me-RK/Wearable-Air-Quality-Pendant/Images/AIQ Monitor Pendant.png

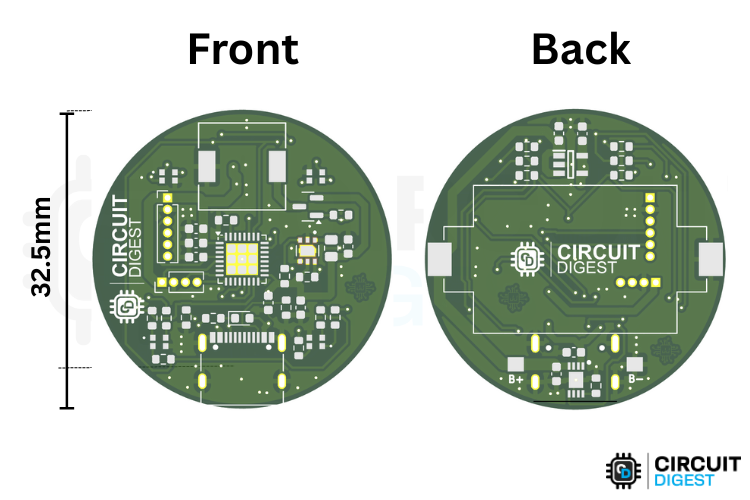
Images/AIQ Monitor Pendant.png
