me-RK/Wearable-Air-Quality-Pendant/Images/RGB Light Circuit &  Buzzer Driver Circuit.png

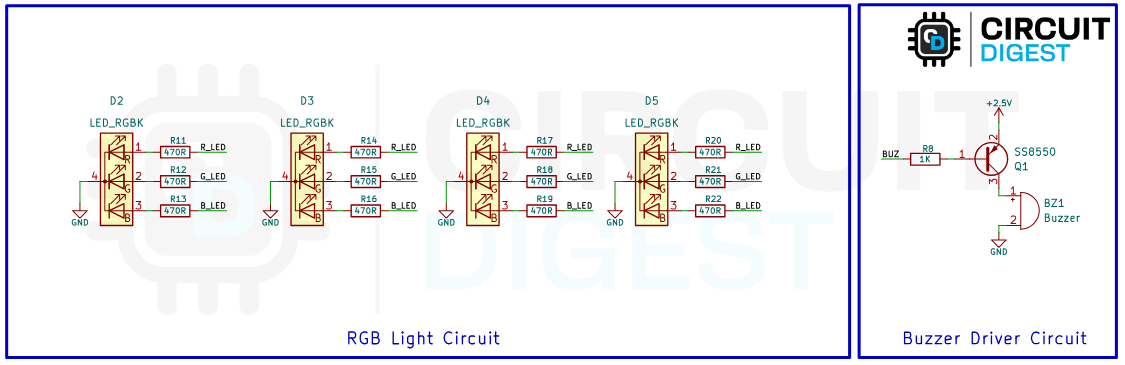
Images/RGB Light Circuit & Buzzer Driver Circuit.png
