me-RK/Wearable-Air-Quality-Pendant/Images/STM32 Programming and IO Circuit.png

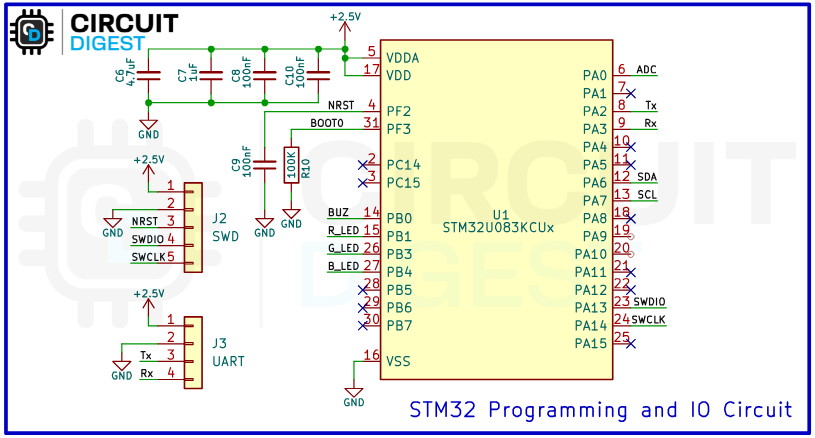
Images/STM32 Programming and IO Circuit.png
