me-RK/Wearable-Air-Quality-Pendant/Images/Title Image.png

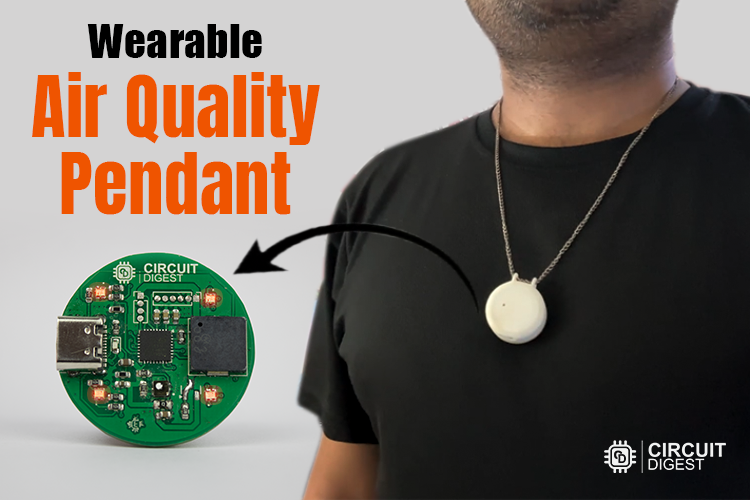
Images/Title Image.png
