me-RK/Wearable-Air-Quality-Pendant/PCB/Wearable-Air-Quality-Pendant/Wearable Air Quality Pendant.png

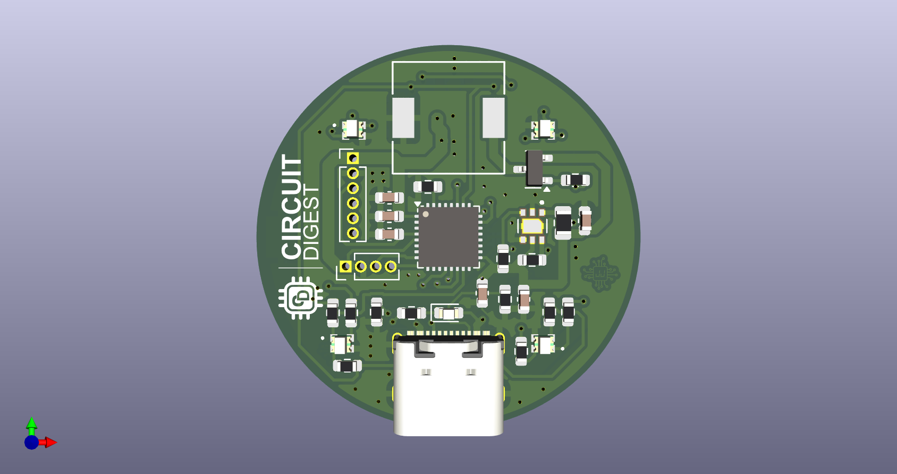
PCB/Wearable-Air-Quality-Pendant/Wearable Air Quality Pendant.png
