me-RK/Wearable-Air-Quality-Pendant/Images/Parts and PCB .png

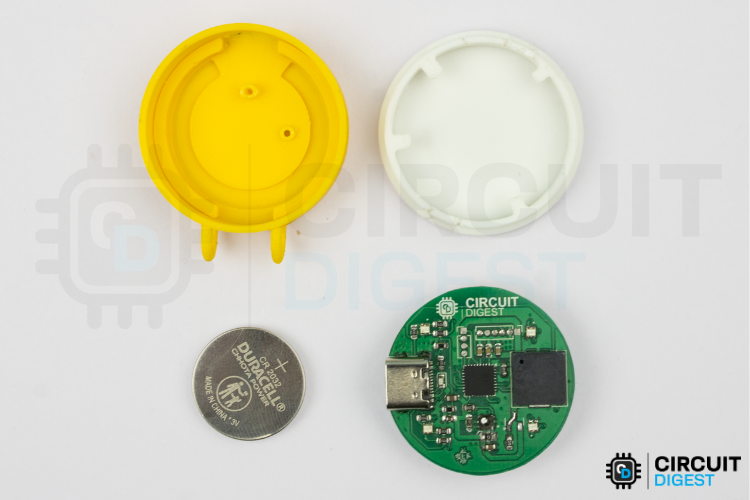
Images/Parts and PCB .png
